andornaut/homeassistant-harmony-control/v1/kicad/ha-harmony-remote/ha-harmony-remote.kicad_pcb

## KiCad design boards/bidirectional_load_switch/pcb/bidirectional_load_switch.kicad_pcb

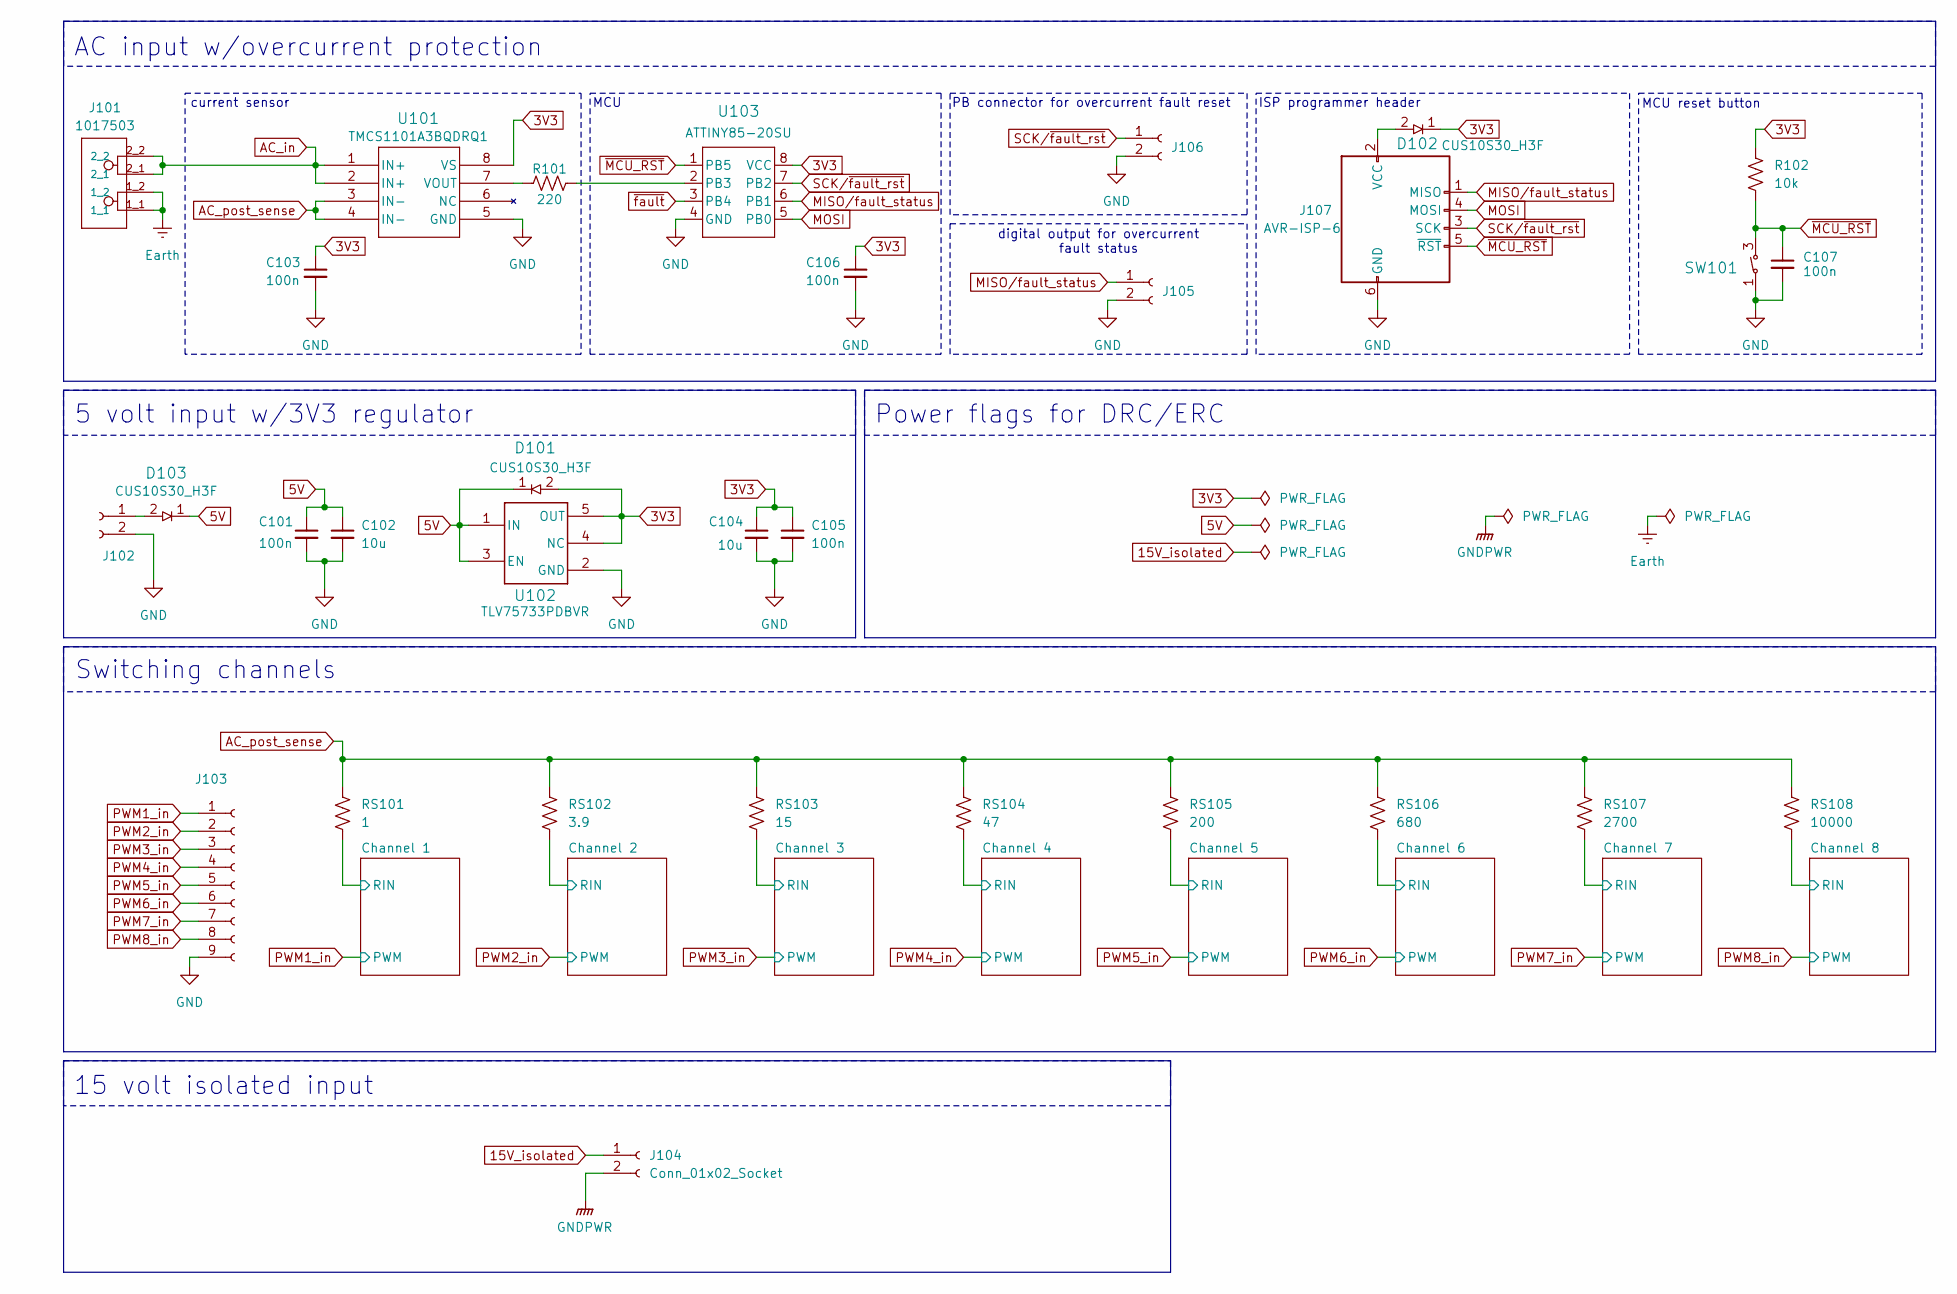
[picture p14: schematic bidirectional_load_switch.kicad_sch, Bidirectional Load Switch]

Parts:
C101, C103, C105, C106, C107: 100n; C_0603_1608Metric
C102, C104: 10u; C_1206_3216Metric
D101, D102, D103: USC_TOS; MPN CUS10S30_H3F
J101: PHOENIX_1017503; PARTREV 22.12.2017
J102, J104, J105, J106: Conn_01x02_Socket; PinHeader_1x02_P2.54mm_Vertical
J103: Conn_01x09_Socket; PinHeader_1x09_P2.54mm_Vertical
J107: AVR-ISP-6; IDC-Header_2x03_P2.54mm_Vertical
R101: 220; R_0603_1608Metric
R102: 10k; R_0603_1608Metric
RS101: 1; R_2512_6332Metric
RS102: 3.9; R_2512_6332Metric
RS103: 15; R_2512_6332Metric
RS104: 47; R_2512_6332Metric
RS105: 200; R_2512_6332Metric
RS106: 680; R_2512_6332Metric
RS107: 2700; R_2512_6332Metric
RS108: 10000; R_2512_6332Metric
SW101: SMT_FS; MPN PTS526 SK15 SMTR2 LFS
U101: SOIC8_D_TEX; MPN TMCS1101A3BQDRQ1
U102: DBV0005A_L; MPN TLV75733PDBVR
U103: 8S2_ATM; MPN ATTINY85-20SU

Connections:
3V3: C103.1, C104.1, C105.1, C106.1, D101.2, D102.1, R102.1, U101.8 (VS), U102.4 (NC), U102.5 (OUT), U103.8 (VCC); also elsewhere on the board
5V: C101.1, C102.1, D101.1, D103.1, U102.1 (IN), U102.3 (EN)
15V_isolated: J104.1; also elsewhere on the board
/Channel 1/RIN: RS101.2; also elsewhere on the board
/Channel 2/RIN: RS102.2; also elsewhere on the board
/Channel 3/RIN: RS103.2; also elsewhere on the board
/Channel 4/RIN: RS104.2; also elsewhere on the board
/Channel 5/RIN: RS105.2; also elsewhere on the board
/Channel 6/RIN: RS106.2; also elsewhere on the board
/Channel 7/RIN: RS107.2; also elsewhere on the board
/Channel 8/RIN: RS108.2; also elsewhere on the board
AC_in: J101.2_1, J101.2_2, U101.1 (IN+), U101.2 (IN+)
AC_post_sense: RS101.1, RS102.1, RS103.1, RS104.1, RS105.1, RS106.1, RS107.1, RS108.1, U101.3 (IN-), U101.4 (IN-)
Earth: J101.1_1, J101.1_2; also elsewhere on the board
GND: C101.2, C102.2, C103.2, C104.2, C105.2, C106.2, C107.2, J102.2, J103.9, J105.2, J106.2, J107.6 (GND), SW101.1, SW101.2, U101.5 (GND), U102.2 (GND), U103.4 (GND); also elsewhere on the board
GNDPWR: J104.2; also elsewhere on the board
MISO/fault_status: J105.1, J107.1 (MISO), U103.6 (PB1)
MOSI: J107.4 (MOSI), U103.5 (PB0)
unnamed: D103.2, J102.1
unnamed: D102.2, J107.2 (VCC)
unnamed: R101.1, U101.7 (VOUT)
unnamed: R101.2, U103.2 (PB3)
PWM1_in: J103.1; also elsewhere on the board
PWM2_in: J103.2; also elsewhere on the board
PWM3_in: J103.3; also elsewhere on the board
PWM4_in: J103.4; also elsewhere on the board
PWM5_in: J103.5; also elsewhere on the board
PWM6_in: J103.6; also elsewhere on the board
PWM7_in: J103.7; also elsewhere on the board
PWM8_in: J103.8; also elsewhere on the board
SCK/~fault_rst: J106.1, J107.3 (SCK), U103.7 (PB2)
~MCU_RST: C107.1, J107.5 (~RST), R102.2, SW101.3, SW101.4, U103.1 (PB5)
~fault: U103.3 (PB4); also elsewhere on the board

Notes on the sheet:
digital output for overcurrent fault status
PB connector for overcurrent fault reset
Power flags for DRC/ERC
MCU
Switching channels
15 volt isolated input
ISP programmer header
MCU reset button
AC input w/overcurrent protection
current sensor
5 volt input w/3V3 regulator

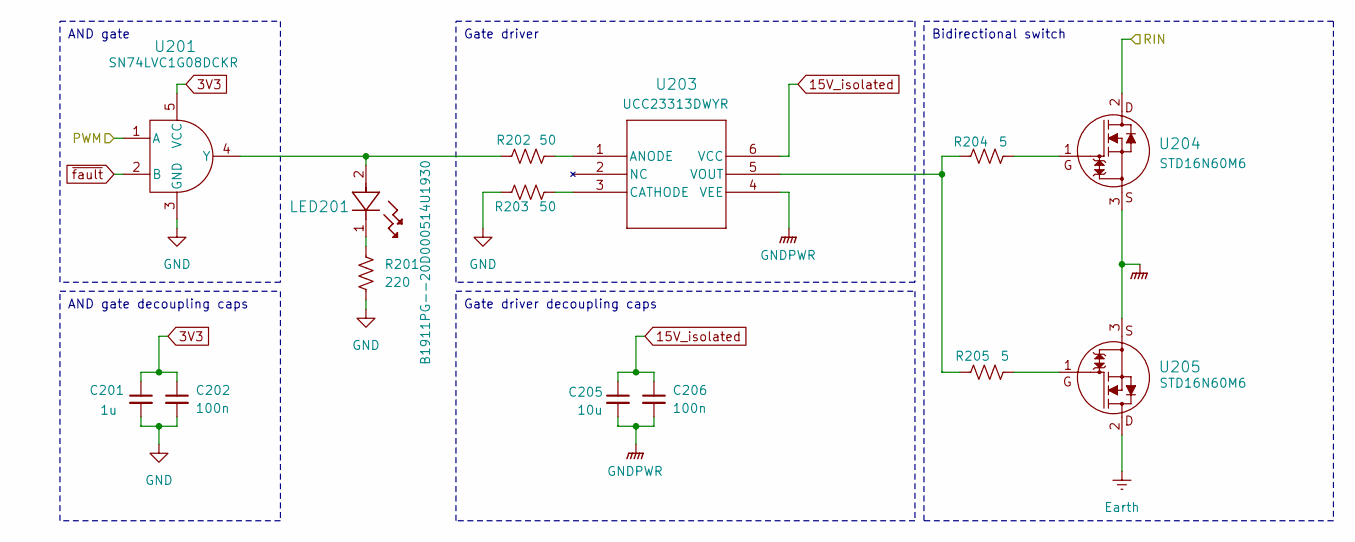
[picture p15: schematic switching_channel.kicad_sch, Bidirectional Load Switch]

Parts:
C201: 1u; C_0603_1608Metric
C202, C206: 100n; C_0603_1608Metric
C205: 10u; C_1206_3216Metric
LED201: LED_B1911PG--20D000514U1930_HVK; MPN B1911PG--20D000514U1930
R201: 220; R_0603_1608Metric
R202, R203: 50; R_0603_1608Metric
R204, R205: 5; R_0805_2012Metric
U201: DCK5; MPN SN74LVC1G08DCKR
U203: SOIC6_DWY_TEX; MPN UCC23313DWYR
U204, U205: DPAKTO-252_STM; MPN STD16N60M6

Connections:
3V3: C201.1, C202.1, U201.5 (VCC); also elsewhere on the board
15V_isolated: C205.1, C206.1, U203.6 (VCC); also elsewhere on the board
/Channel 1/RIN: U204.2; also elsewhere on the board
Earth: U205.2; also elsewhere on the board
GND: C201.2, C202.2, R201.2, R203.1, U201.3 (GND); also elsewhere on the board
GNDPWR: C205.2, C206.2, U203.4 (VEE), U204.3, U205.3; also elsewhere on the board
unnamed: LED201.1, R201.1
unnamed: R204.2, U204.1
unnamed: R205.2, U205.1
unnamed: LED201.2, R202.1, U201.4 (Y)
unnamed: R202.2, U203.1 (ANODE)
unnamed: R203.2, U203.3 (CATHODE)
unnamed: R204.1, R205.1, U203.5 (VOUT)
PWM1_in: U201.1 (A); also elsewhere on the board
~fault: U201.2 (B); also elsewhere on the board

Parts of its further copies:
C301, C401, C501, C601, C701, C801, C901: 1u; C_0603_1608Metric
C302, C306, C402, C406, C502, C506, C602, C606, C702, C706, C802, C806, C902, C906: 100n; C_0603_1608Metric
C305, C405, C505, C605, C705, C805, C905: 10u; C_1206_3216Metric
LED301, LED401, LED501, LED601, LED701, LED801, LED901: LED_B1911PG--20D000514U1930_HVK; MPN B1911PG--20D000514U1930
R301, R401, R501, R601, R701, R801, R901: 220; R_0603_1608Metric
R302, R303, R402, R403, R502, R503, R602, R603, R702, R703, R802, R803, R902, R903: 50; R_0603_1608Metric
R304, R305, R404, R405, R504, R505, R604, R605, R704, R705, R804, R805, R904, R905: 5; R_0805_2012Metric
U301, U401, U501, U601, U701, U801, U901: DCK5; MPN SN74LVC1G08DCKR
U303, U403, U503, U603, U703, U803, U903: SOIC6_DWY_TEX; MPN UCC23313DWYR
U304, U305, U404, U405, U504, U505, U604, U605, U704, U705, U804, U805, U904, U905: DPAKTO-252_STM; MPN STD16N60M6

Connections of its further copies:
3V3: C301.1, C302.1, C401.1, C402.1, C501.1, C502.1, C601.1, C602.1, C701.1, C702.1, C801.1, C802.1, C901.1, C902.1, U301.5 (VCC), U401.5 (VCC), U501.5 (VCC), U601.5 (VCC), U701.5 (VCC), U801.5 (VCC), U901.5 (VCC); also elsewhere on the board
15V_isolated: C305.1, C306.1, C405.1, C406.1, C505.1, C506.1, C605.1, C606.1, C705.1, C706.1, C805.1, C806.1, C905.1, C906.1, U303.6 (VCC), U403.6 (VCC), U503.6 (VCC), U603.6 (VCC), U703.6 (VCC), U803.6 (VCC), U903.6 (VCC); also elsewhere on the board
/Channel 2/RIN: U304.2; also elsewhere on the board
/Channel 3/RIN: U404.2; also elsewhere on the board
/Channel 4/RIN: U504.2; also elsewhere on the board
/Channel 5/RIN: U604.2; also elsewhere on the board
/Channel 6/RIN: U704.2; also elsewhere on the board
/Channel 7/RIN: U804.2; also elsewhere on the board
/Channel 8/RIN: U904.2; also elsewhere on the board
Earth: U305.2, U405.2, U505.2, U605.2, U705.2, U805.2, U905.2; also elsewhere on the board
GND: C301.2, C302.2, C401.2, C402.2, C501.2, C502.2, C601.2, C602.2, C701.2, C702.2, C801.2, C802.2, C901.2, C902.2, R301.2, R303.1, R401.2, R403.1, R501.2, R503.1, R601.2, R603.1, R701.2, R703.1, R801.2, R803.1, R901.2, R903.1, U301.3 (GND), U401.3 (GND), U501.3 (GND), U601.3 (GND), U701.3 (GND), U801.3 (GND), U901.3 (GND); also elsewhere on the board
GNDPWR: C305.2, C306.2, C405.2, C406.2, C505.2, C506.2, C605.2, C606.2, C705.2, C706.2, C805.2, C806.2, C905.2, C906.2, U303.4 (VEE), U304.3, U305.3, U403.4 (VEE), U404.3, U405.3, U503.4 (VEE), U504.3, U505.3, U603.4 (VEE), U604.3, U605.3, U703.4 (VEE), U704.3, U705.3, U803.4 (VEE), U804.3, U805.3, U903.4 (VEE), U904.3, U905.3; also elsewhere on the board
unnamed: LED301.1, R301.1
unnamed: LED401.1, R401.1
unnamed: LED501.1, R501.1
unnamed: LED601.1, R601.1
unnamed: LED701.1, R701.1
unnamed: LED801.1, R801.1
unnamed: LED901.1, R901.1
unnamed: R304.2, U304.1
unnamed: R305.2, U305.1
unnamed: R404.2, U404.1
unnamed: R405.2, U405.1
unnamed: R504.2, U504.1
unnamed: R505.2, U505.1
unnamed: R604.2, U604.1
unnamed: R605.2, U605.1
unnamed: R704.2, U704.1
unnamed: R705.2, U705.1
unnamed: R804.2, U804.1
unnamed: R805.2, U805.1
unnamed: R904.2, U904.1
unnamed: R905.2, U905.1
unnamed: LED301.2, R302.1, U301.4 (Y)
unnamed: R302.2, U303.1 (ANODE)
unnamed: R303.2, U303.3 (CATHODE)
unnamed: R304.1, R305.1, U303.5 (VOUT)
unnamed: LED401.2, R402.1, U401.4 (Y)
unnamed: R402.2, U403.1 (ANODE)
unnamed: R403.2, U403.3 (CATHODE)
unnamed: R404.1, R405.1, U403.5 (VOUT)
unnamed: LED501.2, R502.1, U501.4 (Y)
unnamed: R502.2, U503.1 (ANODE)
unnamed: R503.2, U503.3 (CATHODE)
unnamed: R504.1, R505.1, U503.5 (VOUT)
unnamed: LED601.2, R602.1, U601.4 (Y)
unnamed: R602.2, U603.1 (ANODE)
unnamed: R603.2, U603.3 (CATHODE)
unnamed: R604.1, R605.1, U603.5 (VOUT)
unnamed: LED701.2, R702.1, U701.4 (Y)
unnamed: R702.2, U703.1 (ANODE)
unnamed: R703.2, U703.3 (CATHODE)
unnamed: R704.1, R705.1, U703.5 (VOUT)
unnamed: LED801.2, R802.1, U801.4 (Y)
unnamed: R802.2, U803.1 (ANODE)
unnamed: R803.2, U803.3 (CATHODE)
unnamed: R804.1, R805.1, U803.5 (VOUT)
unnamed: LED901.2, R902.1, U901.4 (Y)
unnamed: R902.2, U903.1 (ANODE)
unnamed: R903.2, U903.3 (CATHODE)
unnamed: R904.1, R905.1, U903.5 (VOUT)
PWM2_in: U301.1 (A); also elsewhere on the board
PWM3_in: U401.1 (A); also elsewhere on the board
PWM4_in: U501.1 (A); also elsewhere on the board
PWM5_in: U601.1 (A); also elsewhere on the board
PWM6_in: U701.1 (A); also elsewhere on the board
PWM7_in: U801.1 (A); also elsewhere on the board
PWM8_in: U901.1 (A); also elsewhere on the board
~fault: U301.2 (B), U401.2 (B), U501.2 (B), U601.2 (B), U701.2 (B), U801.2 (B), U901.2 (B); also elsewhere on the board

Notes on the sheet:
Gate driver
Bidirectional switch
Gate driver decoupling caps
AND gate decoupling caps
AND gate

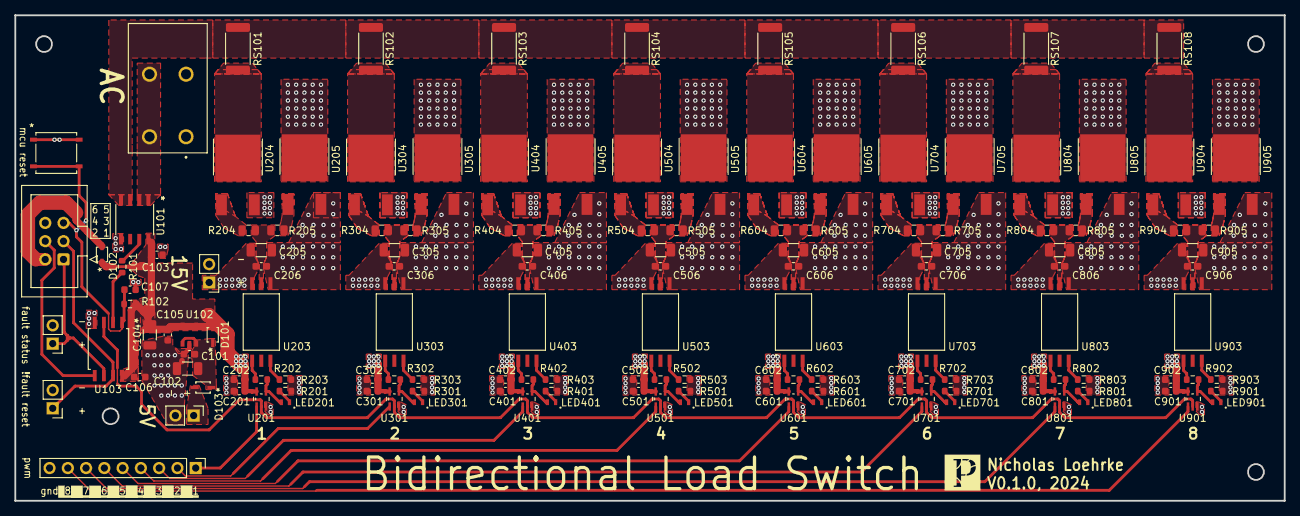
[picture p16: board bidirectional_load_switch.kicad_pcb from above]

Board: 2 copper layers, 176.5 x 67.5 mm, 143 parts (0 on the bottom side), 89 nets.
